c3d2/pentabug/img/rawimg/20120831_001.jpg

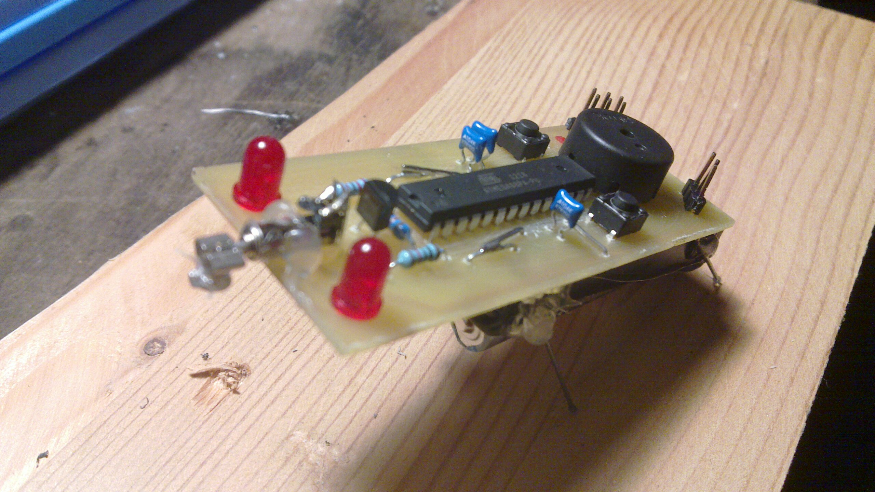
img/rawimg/20120831_001.jpg
