c3d2/pentabug/img/rawimg/20120831_002.jpg

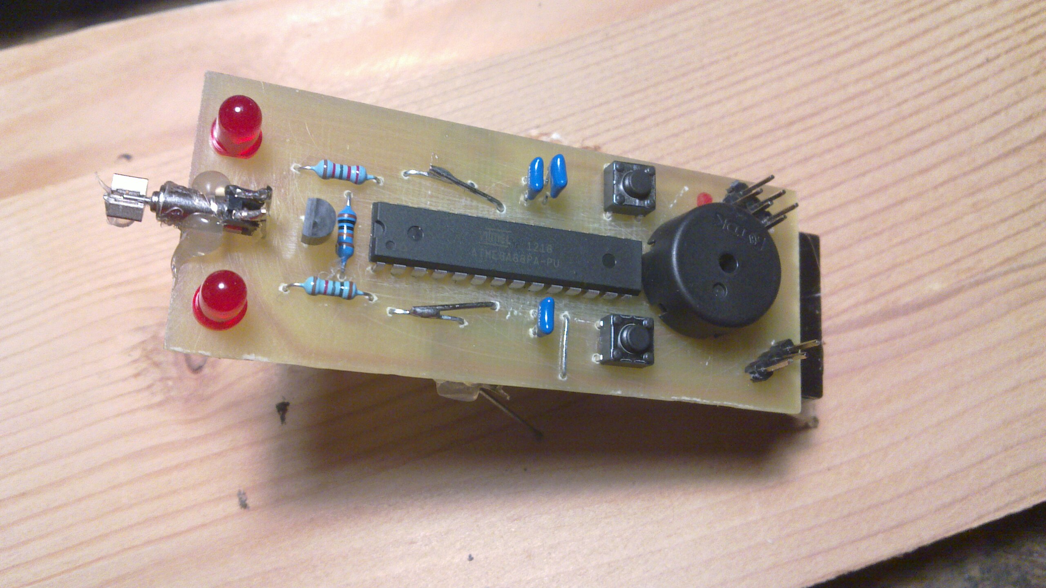
img/rawimg/20120831_002.jpg
