c3d2/pentabug/img/rawimg/20120831_004.jpg

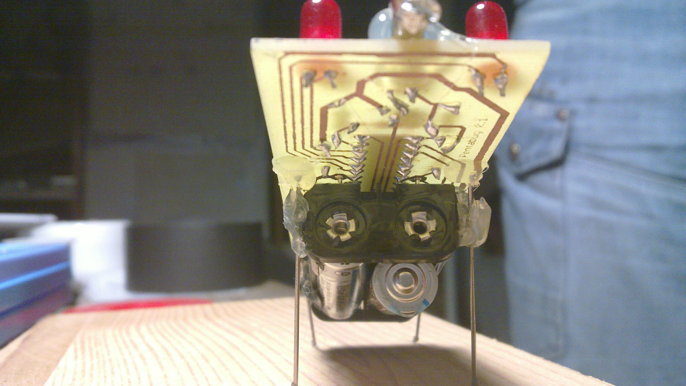
img/rawimg/20120831_004.jpg
