c3d2/pentabug/img/rawimg/20121226_001.jpg

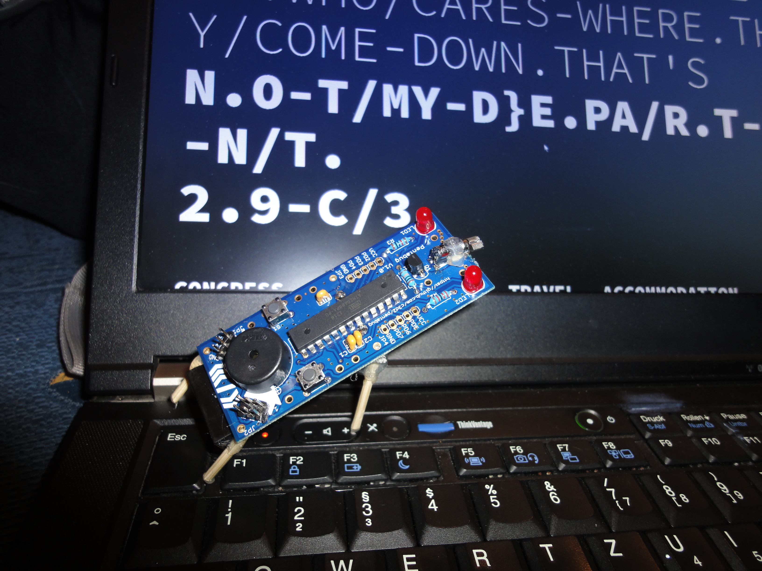
img/rawimg/20121226_001.jpg
