c3d2/pentabug/img/rawimg/20121226_002.jpg

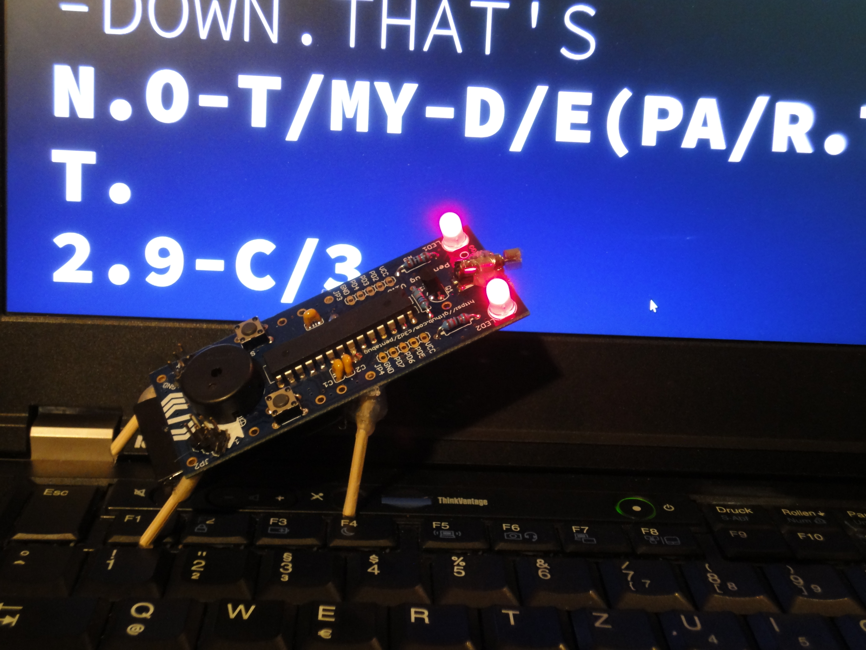
img/rawimg/20121226_002.jpg
