c3d2/pentabug/img/29c3bug_400x350.jpg

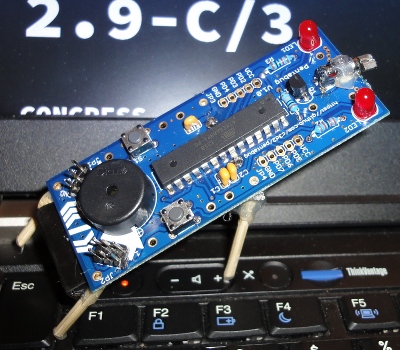
img/29c3bug_400x350.jpg
